Alienor134/UC2_Fluorescence_microscope/assets/images/A.png

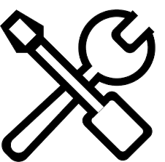
assets/images/A.png
