Alienor134/UC2_Fluorescence_microscope/assets/images/Application_Fluorescence_Microscope_Infinity_cellstorm_v3.png

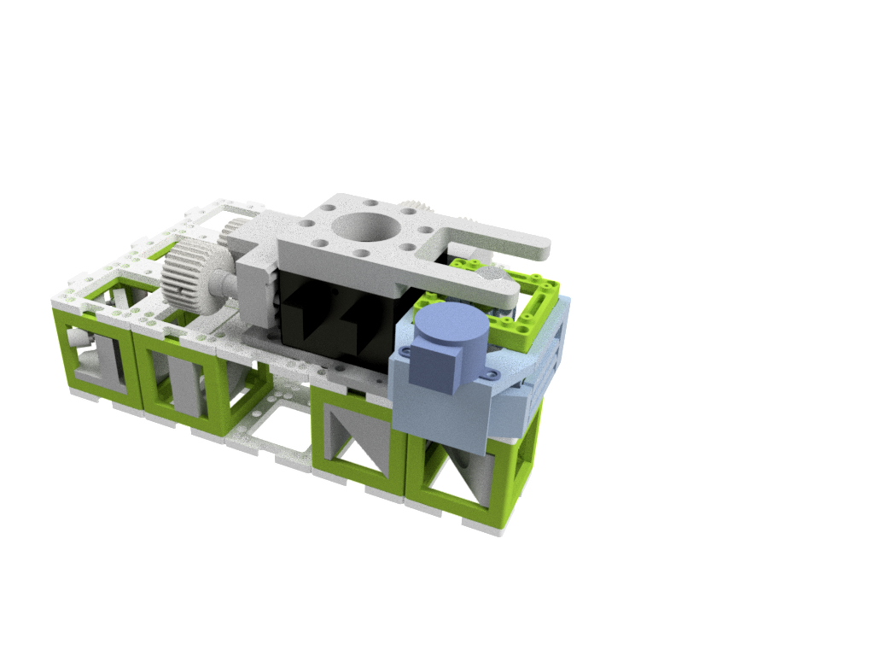
assets/images/Application_Fluorescence_Microscope_Infinity_cellstorm_v3.png
