Alienor134/UC2_Fluorescence_microscope/assets/images/B.png

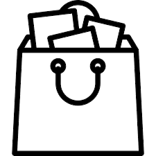
assets/images/B.png
