Alienor134/UC2_Fluorescence_microscope/assets/images/cover.jpg

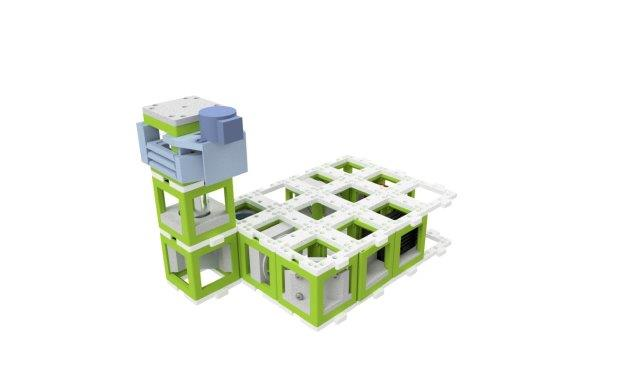
assets/images/cover.jpg
