Alienor134/UC2_Fluorescence_microscope/assets/images/D.png

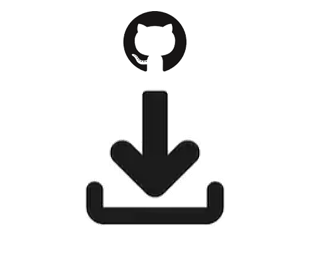
assets/images/D.png
