Alienor134/UC2_Fluorescence_microscope/assets/images/IMG_20211126_092207.jpg

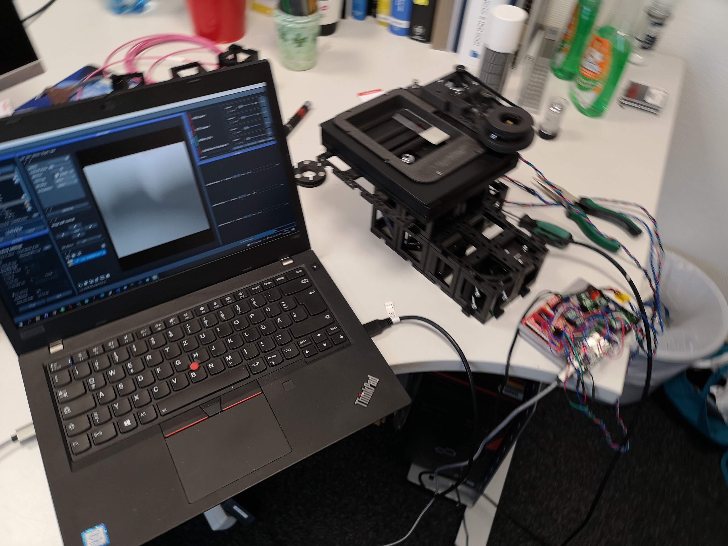
assets/images/IMG_20211126_092207.jpg
