Alienor134/UC2_Fluorescence_microscope/assets/images/P.png

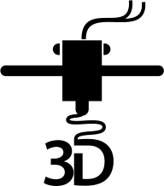
assets/images/P.png
