Alienor134/UC2_Fluorescence_microscope/assets/images/photo_second_part.jpg

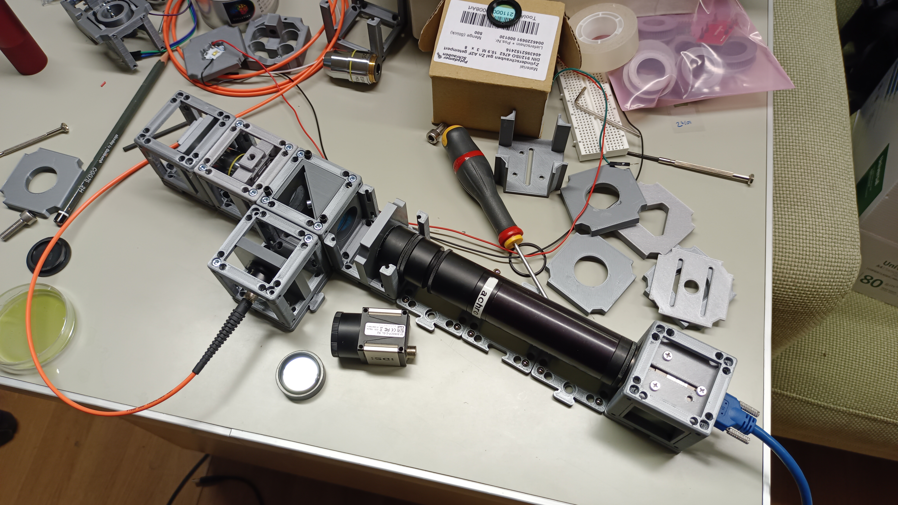
assets/images/photo_second_part.jpg
