Alienor134/UC2_Fluorescence_microscope/assets/images/RECOM.png

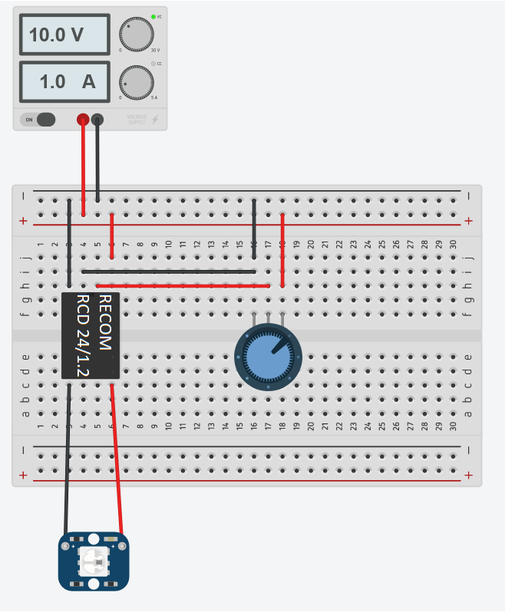
assets/images/RECOM.png
