Alienor134/UC2_Fluorescence_microscope/assets/images/S.png

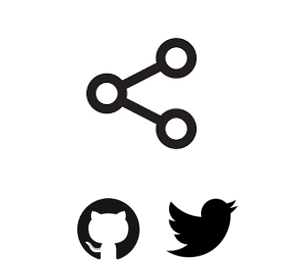
assets/images/S.png
