Alienor134/UC2_Fluorescence_microscope/assets/images/software.png

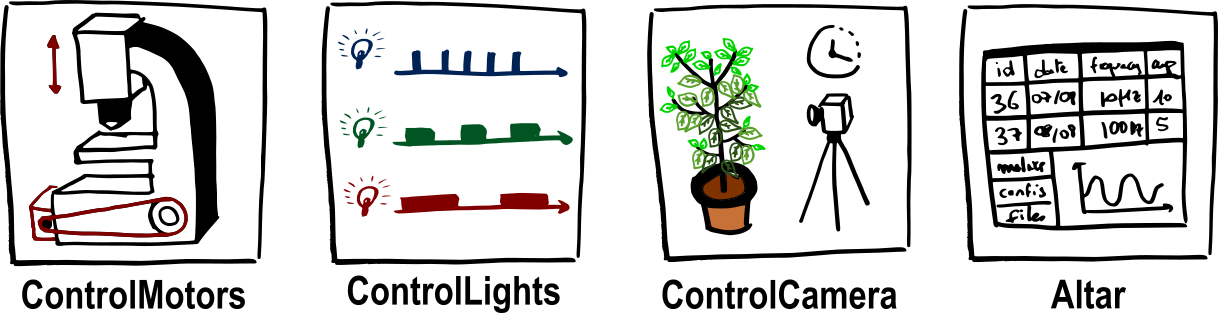
assets/images/software.png
