Alienor134/UC2_Fluorescence_microscope/assets/images/vimba_3.png

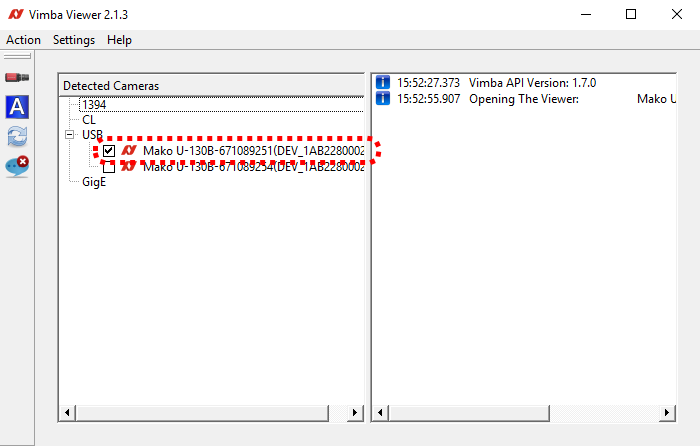
assets/images/vimba_3.png
