Alienor134/UC2_Fluorescence_microscope/STL/motor_holder/3DView-2.png

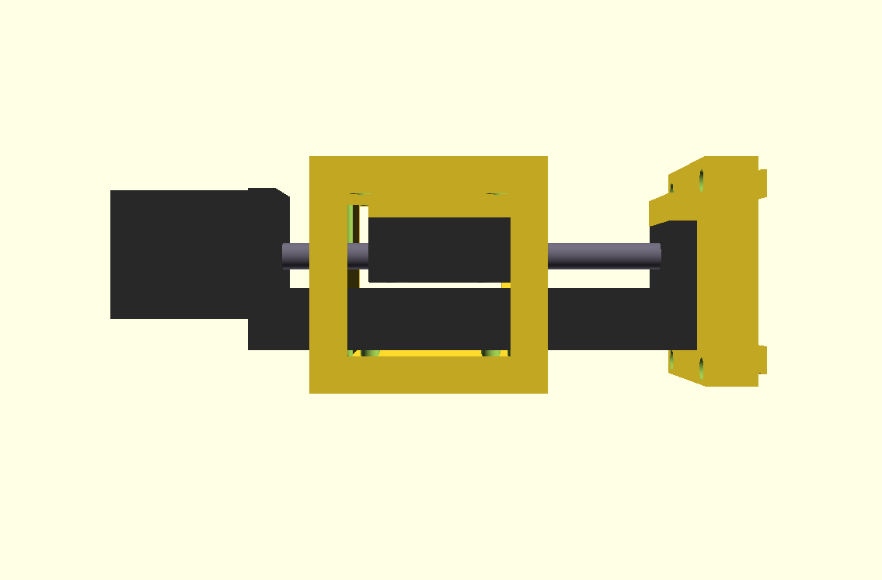
STL/motor_holder/3DView-2.png
