Alienor134/UC2_Fluorescence_microscope/STL/motor_holder/3DView.png

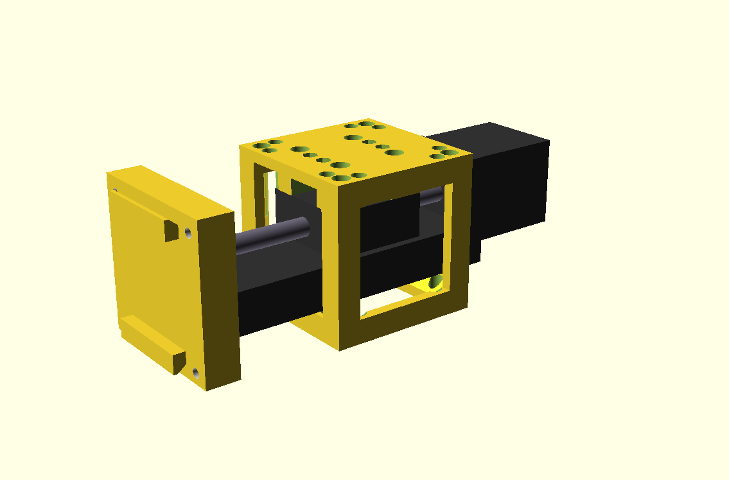
STL/motor_holder/3DView.png
