Alienor134/UC2_Fluorescence_microscope/STL/motor_holder/FrontPanel.png

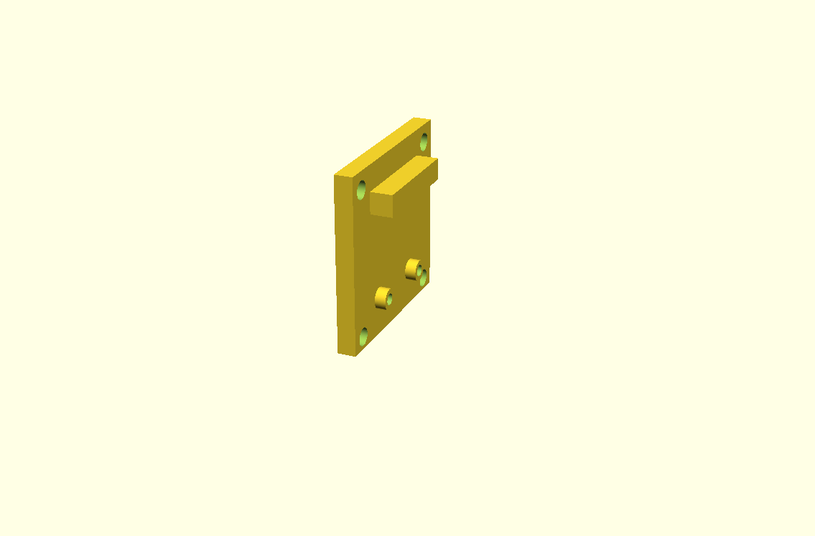
STL/motor_holder/FrontPanel.png
