Alienor134/UC2_Fluorescence_microscope/STL/motor_holder/SampleHolder.png

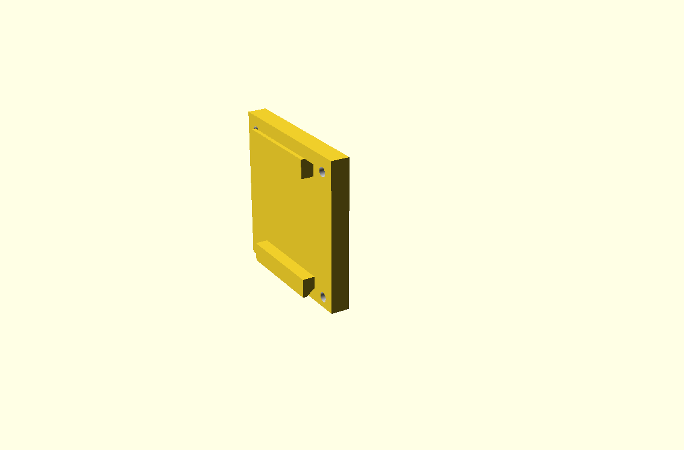
STL/motor_holder/SampleHolder.png
