Alienor134/UC2_Fluorescence_microscope/STL/motor_holder/slider.jpg

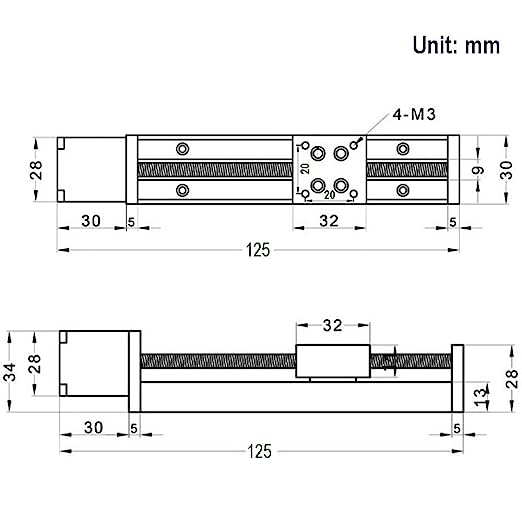
STL/motor_holder/slider.jpg
