Alienor134/UC2_Fluorescence_microscope/STL/motor_holder/StructureTop.png

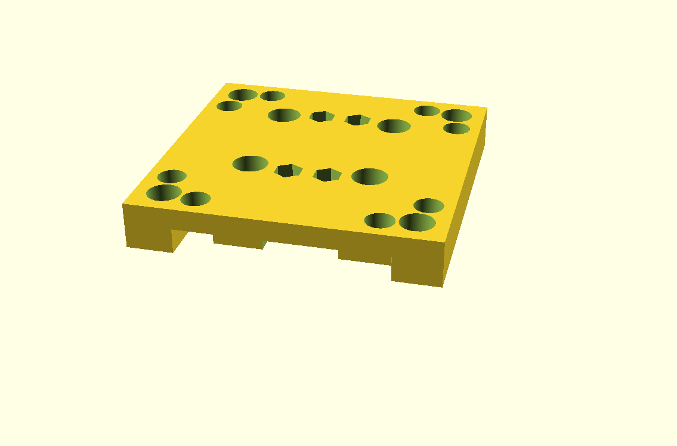
STL/motor_holder/StructureTop.png
