Alienor134/UC2_Fluorescence_microscope/STL/beamsplitter/20_Cube_Insert_Beamsplittercube_Retainring_25mm_v3.stl

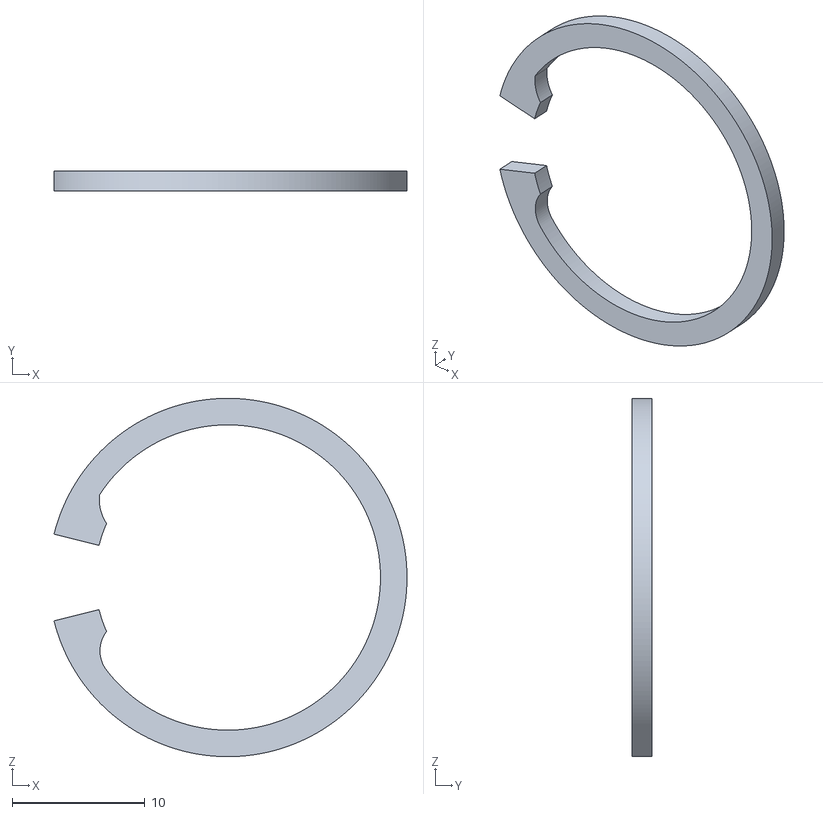
[picture p52: CAD file, 2022-05-24]
STL/beamsplitter/20_Cube_Insert_Beamsplittercube_Retainring_25mm_v3.stl
26.6 x 1.50 x 27.0
