Alienor134/UC2_Fluorescence_microscope/STL/motor_holder/SampleHolderRail.dxf

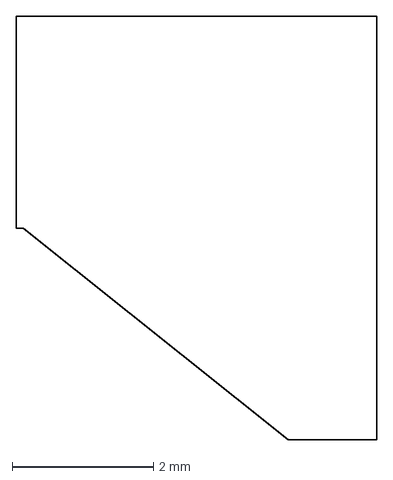
[picture p53: CAD file, 2026-02-03]
STL/motor_holder/SampleHolderRail.dxf
5.10 x 6.00 mm
