Alienor134/UC2_Fluorescence_microscope/STL/objective_holder/20_Cube_Insert_Sample_clamp_v3.stl

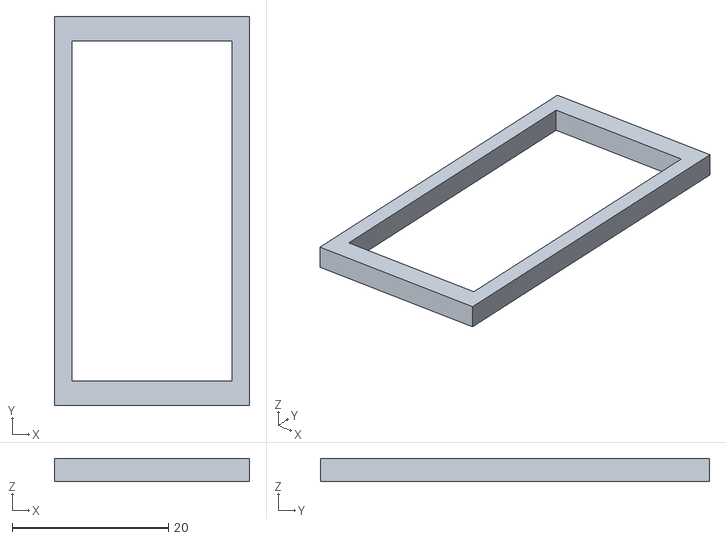
[picture p54: CAD file, 2022-05-24]
STL/objective_holder/20_Cube_Insert_Sample_clamp_v3.stl
25.0 x 49.8 x 3.00
