Alienor134/UC2_Fluorescence_microscope/STL/motor_holder/FrontPanel.stl

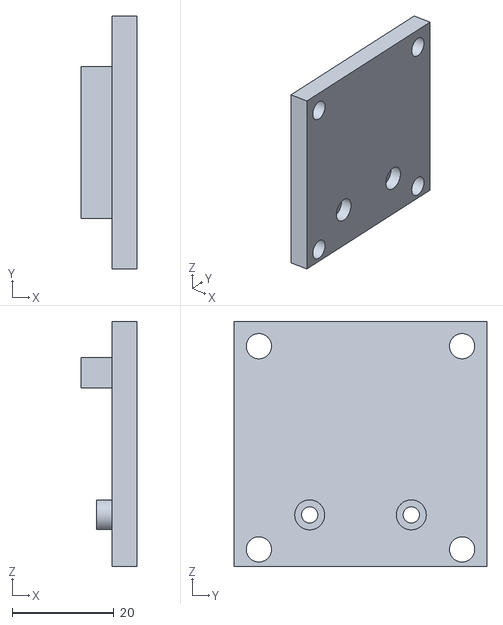
[picture p55: CAD file, 2026-02-03]
STL/motor_holder/FrontPanel.stl
11.1 x 49.8 x 48.3
