Alienor134/UC2_Fluorescence_microscope/STL/motor_holder/LinearSlider.dxf

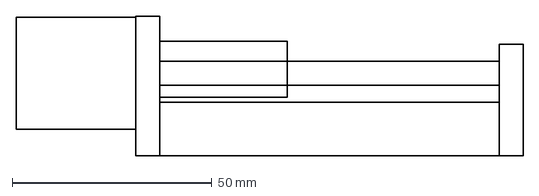
[picture p56: CAD file, 2026-02-03]
STL/motor_holder/LinearSlider.dxf
127.0 x 35.0 mm
